sean44104/Removable-Gate-OEM/Images/pnb3.png

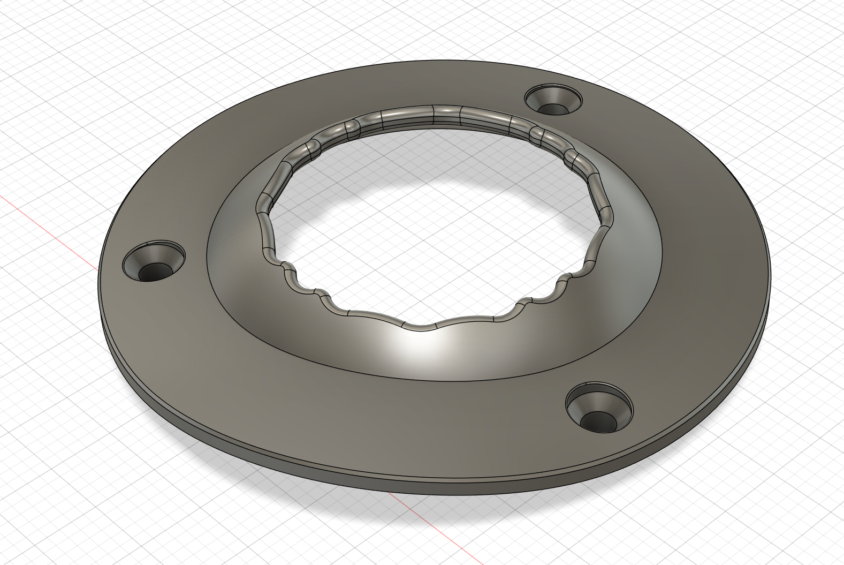
Images/pnb3.png
