sean44104/Removable-Gate-OEM/Images/rpg1.png

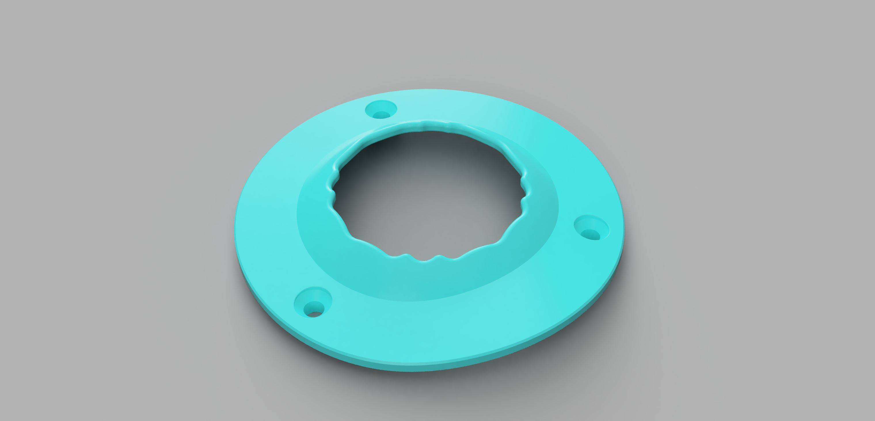
Images/rpg1.png
