sean44104/Removable-Gate-OEM/Images/rpg2.png

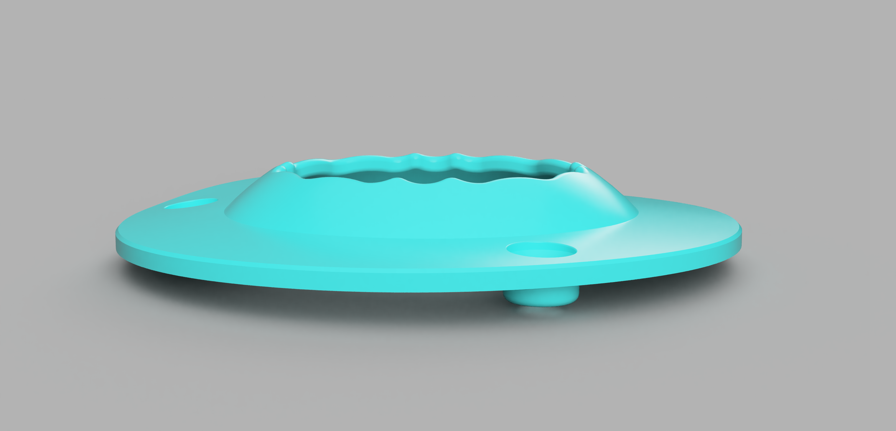
Images/rpg2.png
